sunswift/sunswift.bms/hardware/module_board/Archived_un-used/1_4/Module_Board_1_4.pdf

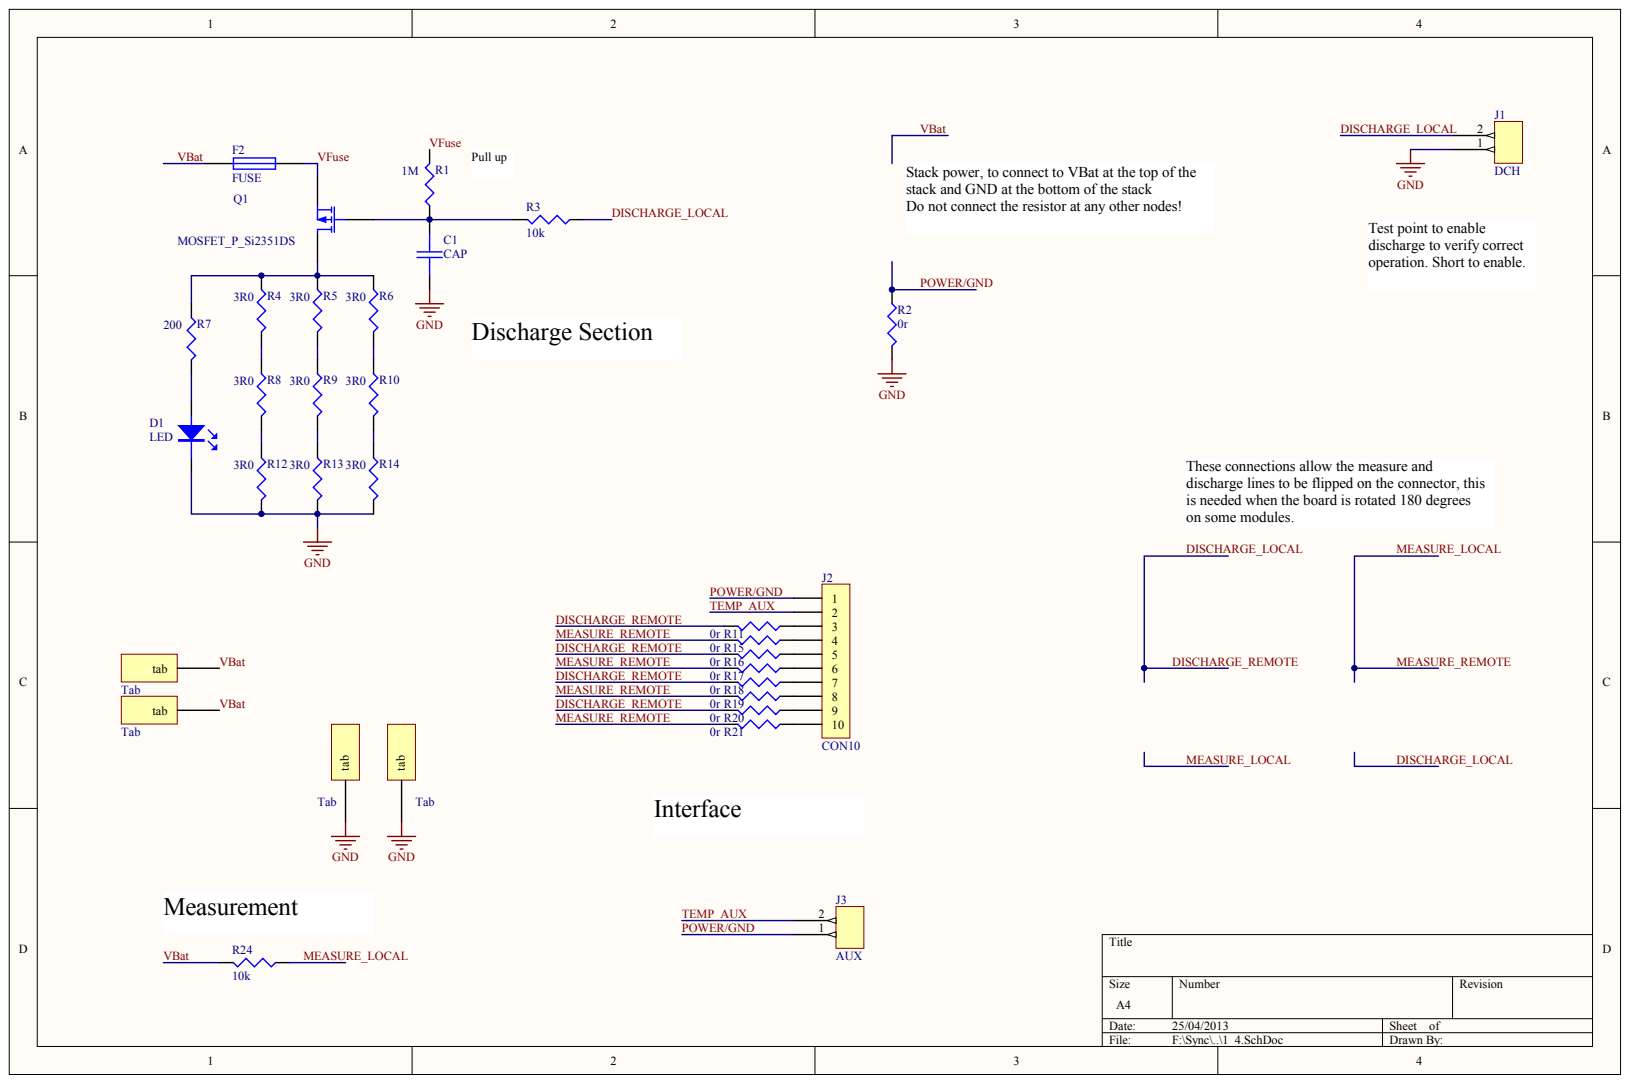
[picture p9: page 1]

Stack pow
stack and GND at the bottom of the stack
Do not

ct to VBat at the top of the

FUS
ct the resistor at any other nodes! Q1

est point to enable
discharge to verify correct
operation. Short to enable

These connections allow the measure and
discharge lines to be
on some modules.

eded when the board is rotated 180 degre

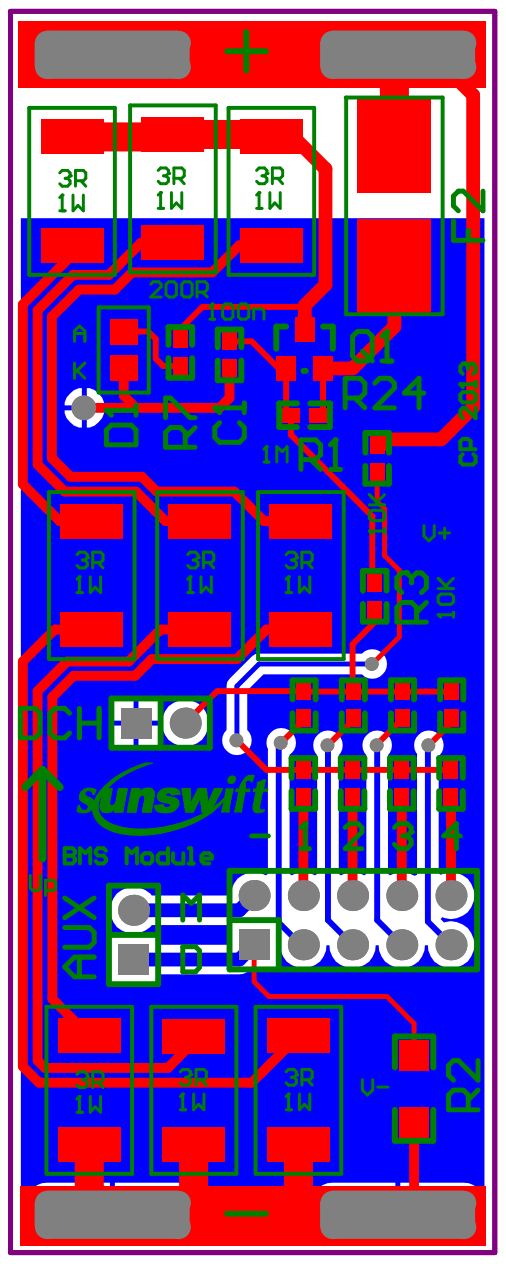
[picture p10: page 2]
