sunswift/sunswift.bms/firmware/include/project/system_LPC11xx.h

/**************************************************************************//**
 * $Id:: system_LPC11xx.h 4785 2010-09-03 22:39:27Z nxp21346              $
 *
 * @file     system_LPC11xx.h
 * @brief    CMSIS Cortex-M0 Device Peripheral Access Layer Header File
 *           for the NXP LPC11xx Device Series
 * @version  V1.00
 * @date     17. November 2009
 *
 * @note
 * Copyright (C) 2009 ARM Limited. All rights reserved.
 *
 * @par
 * ARM Limited (ARM) is supplying this software for use with Cortex-M 
 * processor based microcontrollers.  This file can be freely distributed 
 * within development tools that are supporting such ARM based processors. 
 *
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
 ******************************************************************************/


#ifndef __SYSTEM_LPC11xx_H
#define __SYSTEM_LPC11xx_H

#ifdef __cplusplus
extern "C" {
#endif

#include <stdint.h>

extern uint32_t SystemCoreClock;     /*!< System Clock Frequency (Core Clock)  */


/**
 * Initialize the system
 *
 * @param  none
 * @return none
 *
 * @brief  Setup the microcontroller system.
 *         Initialize the System and update the SystemCoreClock variable.
 */
#define CONFIG_ENABLE_CMSIS_SYSTEMINIT				1
extern void SystemInit (void);

/**
 * Update SystemCoreClock variable
 *
 * @param  none
 * @return none
 *
 * @brief  Updates the SystemCoreClock with current core Clock 
 *         retrieved from cpu registers.
 */
#define CONFIG_ENABLE_CMSIS_SYSTEMCORECLOCKUPDATE	1
//#define CONFIG_CMSIS_SET_SYSTEMCORECLOCK_DEFAULT	48000000
extern void SystemCoreClockUpdate (void);

/*
//-------- <<< Use Configuration Wizard in Context Menu >>> ------------------
*/

/*--------------------- Clock Configuration ----------------------------------
//
// <e> Clock Configuration
//   <e1> System Clock Setup
//     <e2> System Oscillator Enable
//       <o3.1> Select System Oscillator Frequency Range
//                     <0=> 1 - 20 MHz
//                     <1=> 15 - 25 MHz
//     </e2>
//     <e4> Watchdog Oscillator Enable
//       <o5.0..4> Select Divider for Fclkana
//                     <0=>   2 <1=>   4 <2=>   6 <3=>   8
//                     <4=>  10 <5=>  12 <6=>  14 <7=>  16
//                     <8=>  18 <9=>  20 <10=> 22 <11=> 24
//                     <12=> 26 <13=> 28 <14=> 30 <15=> 32
//                     <16=> 34 <17=> 36 <18=> 38 <19=> 40
//                     <20=> 42 <21=> 44 <22=> 46 <23=> 48
//                     <24=> 50 <25=> 52 <26=> 54 <27=> 56
//                     <28=> 58 <29=> 60 <30=> 62 <31=> 64
//       <o5.5..8> Select Watchdog Oscillator Analog Frequency (Fclkana)
//                     <0=> Disabled
//                     <1=> 0.5 MHz
//                     <2=> 0.8 MHz
//                     <3=> 1.1 MHz
//                     <4=> 1.4 MHz
//                     <5=> 1.6 MHz
//                     <6=> 1.8 MHz
//                     <7=> 2.0 MHz
//                     <8=> 2.2 MHz
//                     <9=> 2.4 MHz
//                     <10=> 2.6 MHz
//                     <11=> 2.7 MHz
//                     <12=> 2.9 MHz
//                     <13=> 3.1 MHz
//                     <14=> 3.2 MHz
//                     <15=> 3.4 MHz
//     </e4>
//     <o6> Select Input Clock for sys_pllclkin (Register: SYSPLLCLKSEL)
//                     <0=> IRC Oscillator
//                     <1=> System Oscillator
//                     <2=> WDT Oscillator
//                     <3=> Invalid
//     <e7> Use System PLL
//                     <i> F_pll = M * F_in
//                     <i> F_in must be in the range of 10 MHz to 25 MHz
//       <o8.0..4>   M: PLL Multiplier Selection
//                     <1-32><#-1>
//       <o8.5..6>   P: PLL Divider Selection
//                     <0=> 2
//                     <1=> 4
//                     <2=> 8
//                     <3=> 16
//       <o8.7>      DIRECT: Direct CCO Clock Output Enable
//       <o8.8>      BYPASS: PLL Bypass Enable
//     </e7>
//     <o9> Select Input Clock for Main clock (Register: MAINCLKSEL)
//                     <0=> IRC Oscillator
//                     <1=> Input Clock to System PLL
//                     <2=> WDT Oscillator
//                     <3=> System PLL Clock Out
//   </e1>
//   <o10.0..7> System AHB Divider <0-255>
//                     <i> 0 = is disabled
//   <o11.0>   SYS Clock Enable
//   <o11.1>   ROM Clock Enable
//   <o11.2>   RAM Clock Enable
//   <o11.3>   FLASHREG Flash Register Interface Clock Enable
//   <o11.4>   FLASHARRAY Flash Array Access Clock Enable
//   <o11.5>   I2C Clock Enable
//   <o11.6>   GPIO Clock Enable
//   <o11.7>   CT16B0 Clock Enable
//   <o11.8>   CT16B1 Clock Enable
//   <o11.9>   CT32B0 Clock Enable
//   <o11.10>  CT32B1 Clock Enable
//   <o11.11>  SSP0 Clock Enable
//   <o11.12>  UART Clock Enable
//   <o11.13>  ADC Clock Enable
//   <o11.15>  WDT Clock Enable
//   <o11.16>  IOCON Clock Enable
//   <o11.18>  SSP1 Clock Enable
//
//   <o12.0..7> SSP0 Clock Divider <0-255>
//                     <i> 0 = is disabled
//   <o13.0..7> UART Clock Divider <0-255>
//                     <i> 0 = is disabled
//   <o14.0..7> SSP1 Clock Divider <0-255>
//                     <i> 0 = is disabled
// </e>
*/
#define CLOCK_SETUP           1
#define SYSCLK_SETUP          1
#define SYSOSC_SETUP          1
#define SYSOSCCTRL_Val        0x00000000
#define WDTOSC_SETUP          0
#define WDTOSCCTRL_Val        0x000000A0
#define SYSPLLCLKSEL_Val      0x00000001
#define SYSPLL_SETUP          1
#define SYSPLLCTRL_Val        0x00000023
#define MAINCLKSEL_Val        0x00000003
#define SYSAHBCLKDIV_Val      0x00000001
#define AHBCLKCTRL_Val        0x0001005F
#define SSP0CLKDIV_Val        0x00000001
#define UARTCLKDIV_Val        0x00000001
#define SSP1CLKDIV_Val        0x00000001

/*--------------------- Memory Mapping Configuration -------------------------
//
// <e> Memory Mapping
//   <o1.0..1> System Memory Remap (Register: SYSMEMREMAP)
//                     <0=> Bootloader mapped to address 0
//                     <1=> RAM mapped to address 0
//                     <2=> Flash mapped to address 0
//                     <3=> Flash mapped to address 0
// </e>
*/
#define MEMMAP_SETUP          0
#define SYSMEMREMAP_Val       0x00000001

/*
//-------- <<< end of configuration section >>> ------------------------------
*/

#ifdef __cplusplus
}
#endif

#endif /* __SYSTEM_LPC11x_H */
